ctlaltdel/SG-2/Firmware/op6daisy/configuration.h

#pragma once
#ifndef CONFIGURATION_H
#define CONFIGURATION_H

#define SAMPLE_RATE  48000
#define BLOCK_SIZE      32
#define NUM_PROGRAMS    1
#define NUM_CHANNELS    1
#define NUM_VOICES      2
#define NUM_OPERATORS    6
#define NUM_ENV_STAGES   4
#define RELEASE_STAGE    3
#define PITCH_RANGE_CENTS     1800 // 1.5 octaves
#define CART_CHECK_INTERVAL 250 

#endif
