ctlaltdel/SG-2/Firmware/op6daisy/Channel.cpp

#include <cmath>
#include "AudioPath.h"
#include "Channel.h"
#include "Program.h"
#include "Voice.h"

static float monoMix[NUM_VOICES][BLOCK_SIZE];

void Channel::reset(const Program *program) {
  mProgram=program;
  mExpression=16383/16384.0f; // (very close to) full volume
  setChannelVolume(90*128);   // about 50% linear gain (-6dB)
  setPan(8192);               // center
  mPitchBendFactor=1.0f;      // no pitch bend
  setPitchBendRange(200);     // 200 cents ~ +/-2 semitones
}

void Channel::addVoice(Voice *v) {
  mVoice[mNumVoices]=v;
  mNumVoices++;
}

void Channel::mixVoicesPrivate(float *stereoMix) {
  // Handle LFO
  float lfo=mLfo.sampleAndUpdate(mProgram->lfo);
  float lfoPmDepth=mProgram->lfoPmDepth;
  float pitchMod=exp2f(lfoPmDepth*lfo)*mPitchBendFactor;
  float lfoAmDepth=mProgram->lfoAmDepth;
  float ampMod=lfoAmDepth*(1.0f-lfo);

  
  // Mix the channel's voices
  const float *monoIn=zeroBuffer;
  for (unsigned i=0; i<mNumVoices; ++i) {
    mVoice[i]->fillBuffer(monoMix[i], monoIn, pitchMod, ampMod);
//    monoIn=monoMix[0];
  }
    // Pan and add to the stereo mix
    for (unsigned i=0; i<BLOCK_SIZE; ++i) {
      float x=monoMix[0][i] + monoMix[1][i];
      stereoMix[2*i] = x*mLeftGain;
      stereoMix[2*i+1] = x*mRightGain;
    }

/*  const float *monoIn=zeroBuffer;

  for (unsigned i=0; i<mNumVoices; ++i) {
    mVoice[i]->fillBuffer(monoMix[i], monoIn, pitchMod, ampMod);

    // Pan and add to the stereo mix
    for (unsigned j=0; j<BLOCK_SIZE; ++j) {
      stereoMix[2*i] += (monoMix[i][j] * mLeftGain);
      stereoMix[2*i+1] += (monoMix[i][j] * mRightGain);
    } 
  }*/
}

void Channel::setPan(unsigned p) {
  // -6dB equal power pan law: mLeftGain^2 + mRightGain^2 = 1
  float theta=(M_PI_2/16383)*p;
  mPanLeft=cosf(theta);
  mPanRight=sinf(theta);
  updateGain();
}

void Channel::setPitchBend(int b) {
  mPitchBendFactor=exp2(b*mPitchBendRange);
}

void Channel::setVoiceAmplitude(unsigned voice_num, float ampl) {
  mVoice[voice_num]->setVoiceAmplitude(ampl);
}

void Channel::setPitchBendRange(unsigned cents) {
  // full pitch bend is +/-8192, a cent is 1/1200 octave
  // both scale factors are brought into mPitchBendRange
  mPitchBendRange=cents/(8192*1200.0f);
}
