ctlaltdel/SG-2/Firmware/op6daisy/Voice.h

#pragma once
#ifndef Voice_H
#define Voice_H

#include "FmOperator.h"

class Channel;
class FmAlgorithm;
struct Program;

class Voice {
 public:
 Voice()
   : mKey{0}, mGate{false}, mTimestamp{0}, mProgram{nullptr}
    { }

  unsigned getKey() const { return mKey; }

  bool isNoteOn() const { return mGate; }

  unsigned getTimestamp() const { return mTimestamp; }
  
  void noteOn(Channel *ch, unsigned key, unsigned velocity, unsigned timestamp);

  void noteOff(unsigned timestamp);

  void setPitchBend(unsigned value);

  void setPitchBendRange(unsigned cents);

  void setVoiceAmplitude(float ampl);

  void fillBuffer(float *monoOut,
		  const float *monoIn,
		  float pitchMod,
		  float ampMod);

 private:
  unsigned char mKey;
  bool mGate;
  float vPitchBendFactor;
  float vPitchBendRange;
  float voiceAmplitude;
  unsigned mTimestamp;
  Channel *mChannel;
  const Program *mProgram;
  const FmAlgorithm *mAlgorithm;
  EnvelopeState mEnvelope{true}; // true=sample envelope once per block
  FmOperator mOp[NUM_OPERATORS];
};

#endif
